thomas-trendsoft/BeerBot/cpp/hardware/DriveMotor.h

#ifndef DRIVEMOTOR_H_
#define DRIVEMOTOR_H_

#define DCM_IN1 1
#define DCM_IN2 7
#define DCM_IN3 11
#define DCM_IN4 10
#define DCM_EN2 9
#define DCM_EN1 0

#define START_VAL 28

//
// driving motor Controller
//
class DriveMotor {

  int dcm1val = START_VAL; // left motor

  int dcm2val = START_VAL; // right motor

  public:
    // default constructor
    DriveMotor();

    // stop driving
    void stop();

    // forward driving
    void forward();

    // backward driving
    void backward();

    // turn left
    void turn_left();

    // turn right
    void turn_right();

    // update motor output value for motor 1
    void setMotorLeftValue(int val);

    // update motor output value for motor 2
    void setMotorRightValue(int val);

    // motor output value for motor 1
    int getMotorLeftValue();

    // motor output value for motor 2
    int getMotorRightValue();
};

#endif
