thomas-trendsoft/BeerBot/cpp/hardware/Distance.cpp

#include <chrono>
#include <iostream>
#include <wiringPi.h>
#include "Distance.h"

using namespace std::chrono;

// default constructor
Distance::Distance() {
  // setup gpio pins
  pinMode(DIST_TRIGGER,OUTPUT);
  pinMode(DIST_ECHO,INPUT);
}

//
// measure
// ------------------------
//
// simple one measurement of the current distance
//
double Distance::measure() {

  // start measure signal
  digitalWrite (DIST_TRIGGER,1);
  delay(5);
  digitalWrite (DIST_TRIGGER,0);

  // save time stamp
  system_clock::time_point start = system_clock::now();
  system_clock::time_point end   = system_clock::now();

  // wait for response to start
  int ev;
  do {
    start = system_clock::now();
    ev = digitalRead(DIST_ECHO);
  } while (ev == 0);

  do {
    end = system_clock::now();
    ev  = digitalRead(DIST_ECHO);
  } while (ev == 1);

  // mit der Schallgeschwindigkeit (34300 cm/s) multiplizieren
  // und durch 2 teilen, da hin und zurueck
  double distance = ((end - start).count() * 0.0000343) / 2.0;

  return distance;
}
